dramoz/kv260-atrover/docs_support/camera.jpg

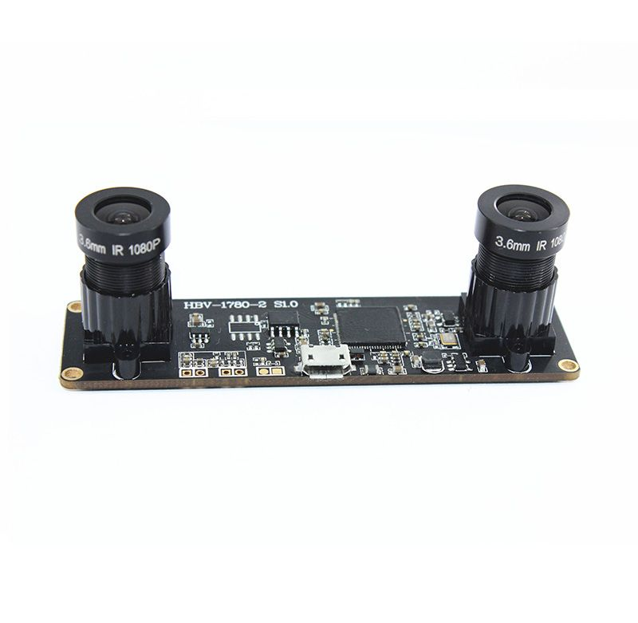
docs_support/camera.jpg
