dramoz/kv260-atrover/docs_support/CHF-GM37-550.jpg

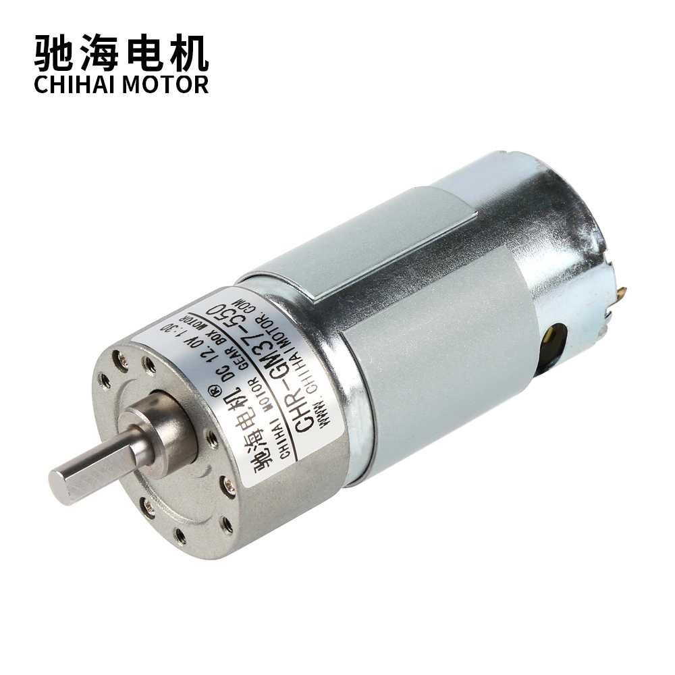
docs_support/CHF-GM37-550.jpg
