dramoz/kv260-atrover/docs_support/dc_motor_driver.jpg

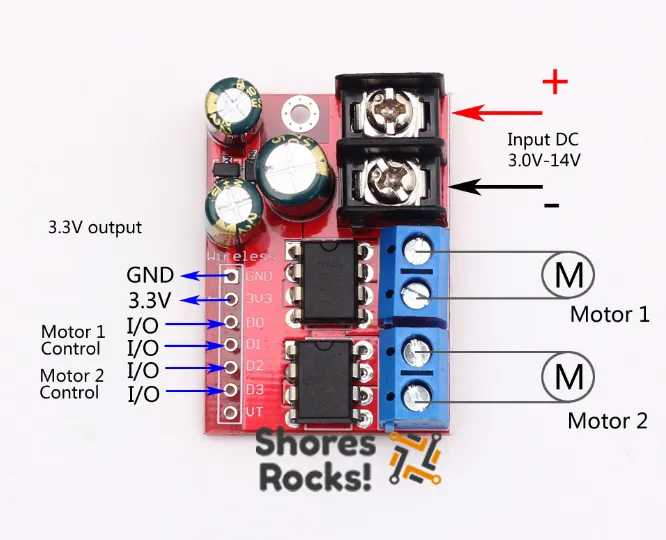
docs_support/dc_motor_driver.jpg
