dramoz/kv260-atrover/docs_support/dc_motor_driver_io.jpg

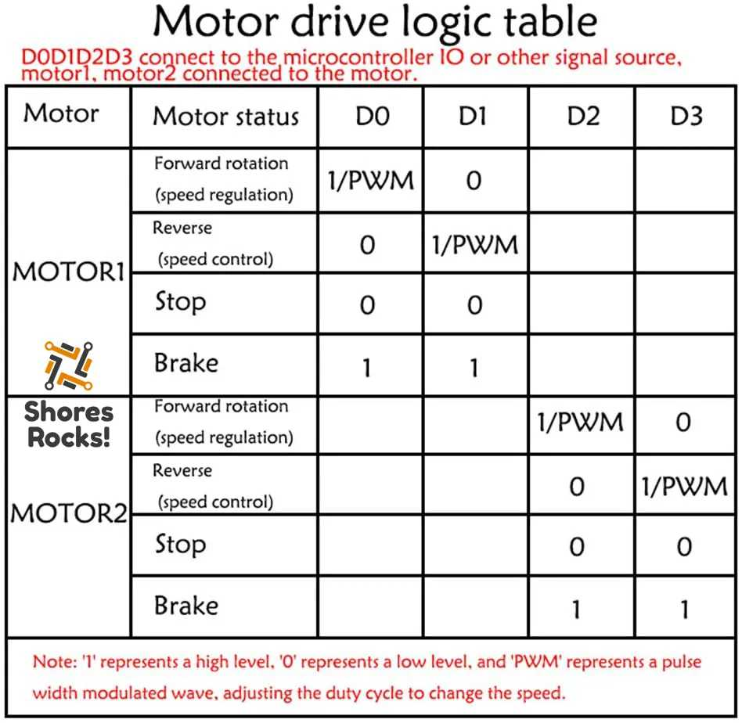
docs_support/dc_motor_driver_io.jpg
