dramoz/kv260-atrover/docs_support/kv260_atrover_0014.jpg

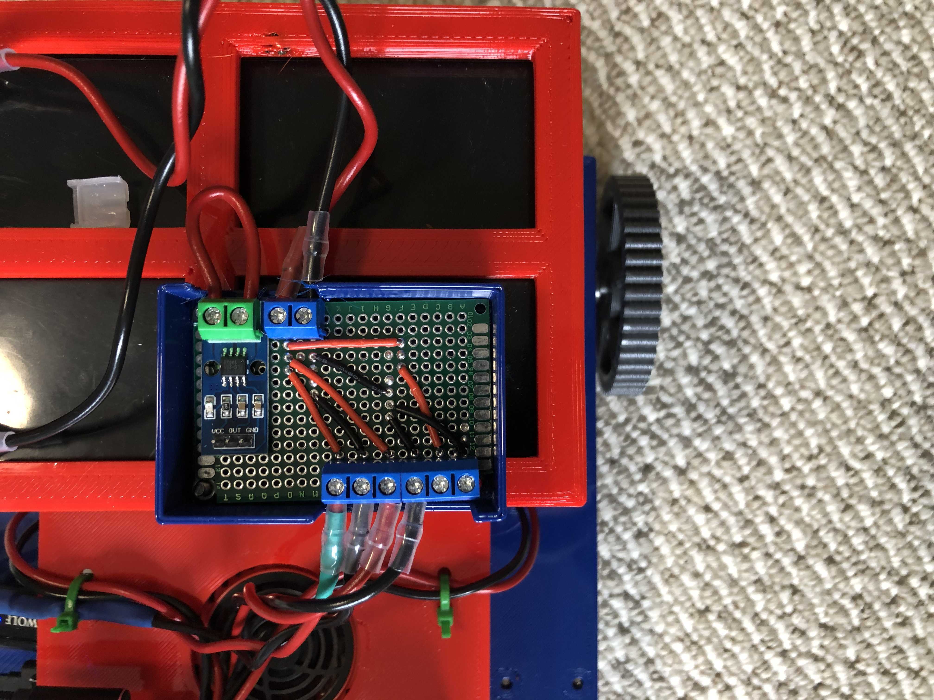
docs_support/kv260_atrover_0014.jpg
