dramoz/kv260-atrover/docs_support/som-connections-600x600.gif

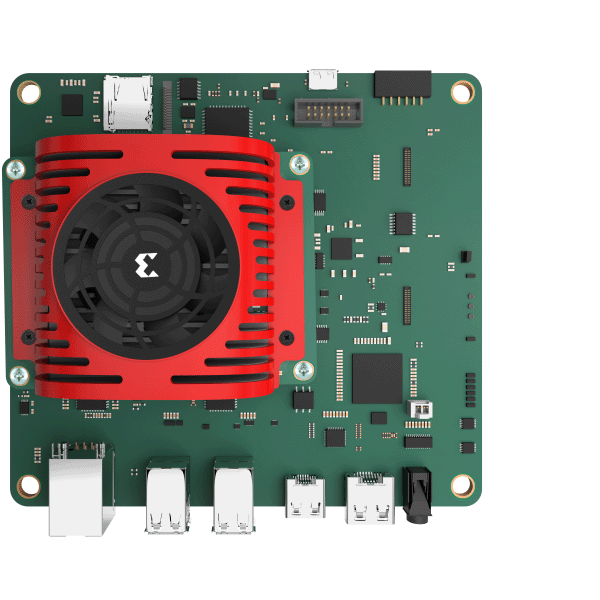
docs_support/som-connections-600x600.gif
