dramoz/kv260-atrover/docs_support/ttgo-t1.jpg

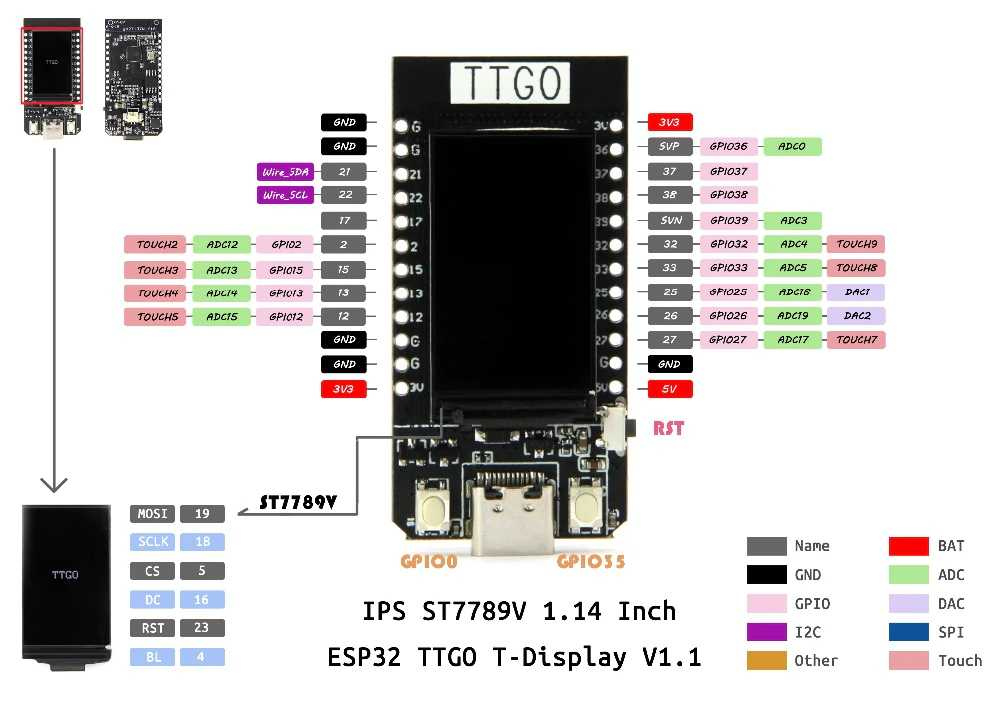
docs_support/ttgo-t1.jpg
