dramoz/kv260-atrover/docs_support/USB_WiFi.jpg

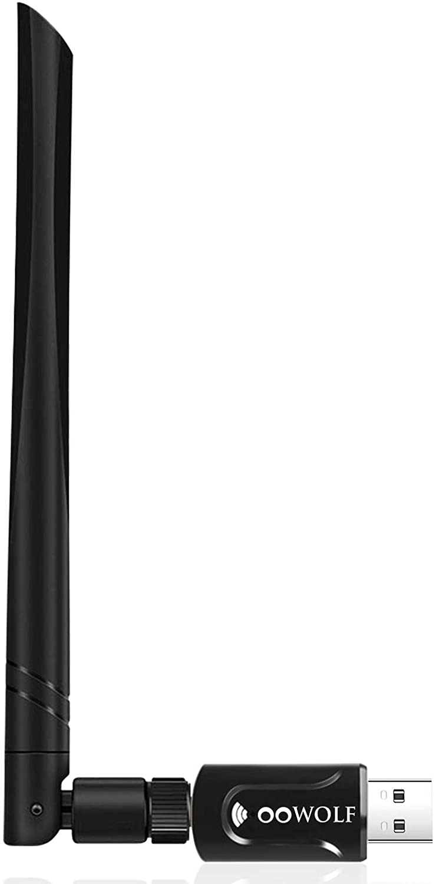
docs_support/USB_WiFi.jpg
