dramoz/kv260-atrover/scripts/camera_calibration_data_gen/images/calibration/w640_h240/lft_7.png

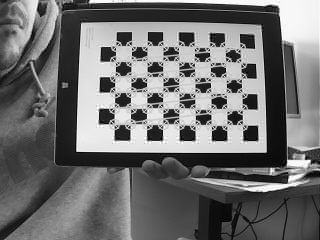
scripts/camera_calibration_data_gen/images/calibration/w640_h240/lft_7.png
