dramoz/kv260-atrover/scripts/camera_calibration_data_gen/images/calibration/w640_h240/rgt_0.png

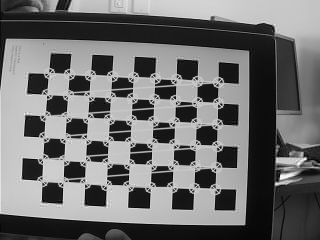
scripts/camera_calibration_data_gen/images/calibration/w640_h240/rgt_0.png
