dramoz/kv260-atrover/scripts/camera_calibration_data_gen/images/calibration/w1280_h480/lft_2.png

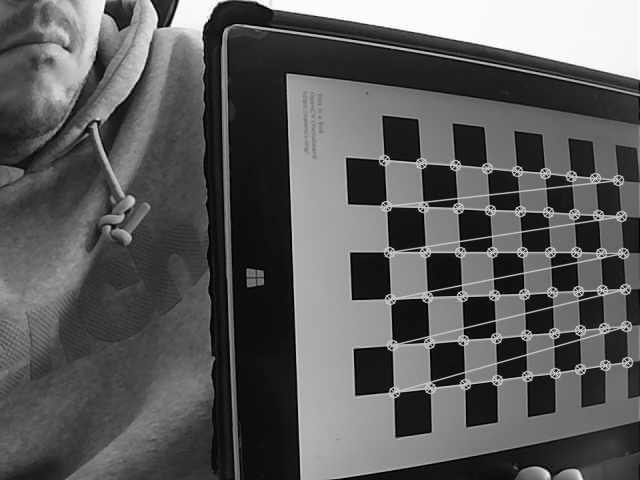
scripts/camera_calibration_data_gen/images/calibration/w1280_h480/lft_2.png
