dramoz/kv260-atrover/scripts/camera_calibration_data_gen/images/calibration/w1280_h480/rgt_5.png

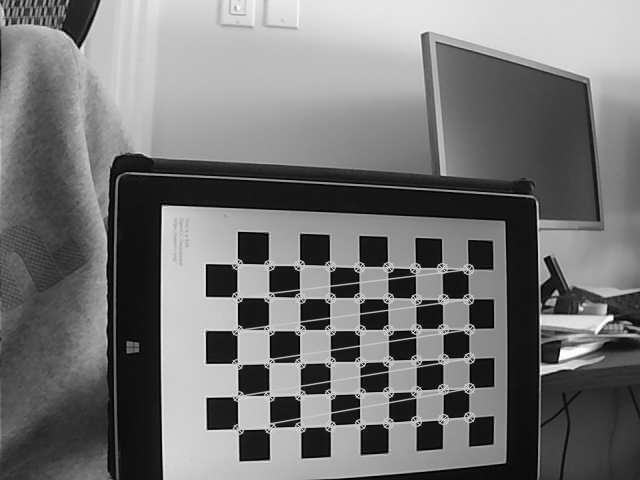
scripts/camera_calibration_data_gen/images/calibration/w1280_h480/rgt_5.png
