dramoz/kv260-atrover/scripts/camera_calibration_data_gen/images/calibration/w2560_h720/rgt_2.png

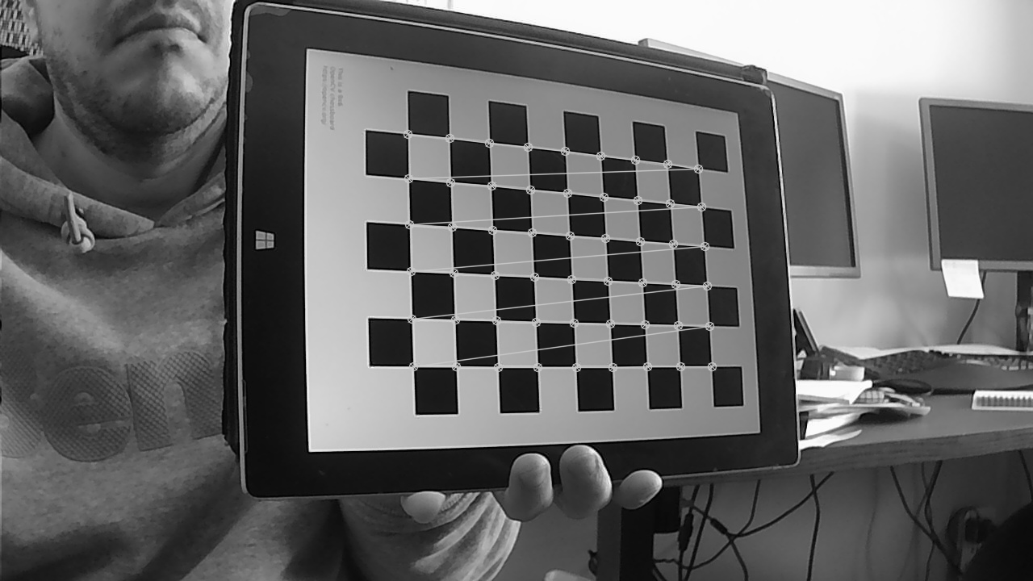
scripts/camera_calibration_data_gen/images/calibration/w2560_h720/rgt_2.png
